nradulovic/hw_parvus/parvus_psu/spice_parvus_psu/ac-detect.asc

C1: cap; 4µ7
C2: cap; 4µ7
C3: cap; 10µ
C4: cap; 10µ
C5: cap; 10µ
C10: polcap; 10m; V=50 Irms=2.5 Rser=0.055 Lser=20n Rpar=40k Cpar=3p
C12: polcap; 10m; V=50 Irms=2.5 Rser=0.055 Lser=20n Rpar=40k Cpar=3p
C22: cap; 470n; Rser=700m Lser=7n Rpar=4.4meg Cpar=1p
C23: cap; 470n; Rser=700m Lser=7n Rpar=4.4meg Cpar=1p
D1: diode; 1N4148
D2: diode; 1N4148
D3: diode; 1N4148
D4: diode; 1N4148
D5: diode; 1N4148
D6: schottky; GBPC3502
D7: LED; QTLP690C
D9: schottky; GBPC3502
D10: schottky; GBPC3502
D11: schottky; GBPC3502
L4: ind; 4n; Rser=1m
L6: ind; 4n; Rser=1m
LGSPK2: ind2; {con1_len*17n}; Rser={con1_len*.5m}
LPWRGND: ind2; {con1_len*7n}; Rser={con1_len*.5m}
LVCC: ind2; {con1_len*7n}; Rser={con1_len*.5m}
LVEE: ind2; {con1_len*27n}; Rser={con1_len*.5m}
Q1: npn; BC546B
Q2: npn; BC546B
Q3: pnp; BC556B
Q4: pnp; BC556B
Q6: npn; BC546B
R1: res; 100k
R2: res; 10k
R3: res; 100k
R4: res; 100k
R5: res; 100
R6: res; {rser}
R7: res; {rser}
R8: res; {rser}
R9: res; {rser}
R10: res; 22k
R11: res; 22k
R12: res; 100k
R13: res; 22k
R14: res; 4k7
R15: res; 10k
R16: res; 2k
R17: res; 18k
R18: res; 25m
R26: res; 25m
R28: res; 15m
R38: res; 25m
R42: res; 10k
R45: res; .47
R46: res; 10k
R50: res; .47
S1: sw
S2: sw
V2: voltage; SINE(0 {supplyVLT*sqrt(2)} 50 1m 0 {phi}); Rser=0
V3: voltage; SINE(0 {supplyVLT*sqrt(2)} 50 1m 0 {phi}); Rser=0
V4: voltage; PULSE(0 20 200m 1n 1n 800m 1.2 2)
Named nets: vcc, vee, gspk, pwrgnd, 0, acs_p, acs_n, vsw, out, stby, mute
.op
.option plotwinsize=0
.option noopiter
Transient
.four {freq} 10 10 v(SPK+,SPK-)
.param prb=0
.param timestep={1/((65536/8)*freq)}
.param freq=50
.param stoptime {iterations/freq}
.ac oct 100 10 100meg
.step param prb list -1 1
AC analysis
.param iterations=80
.param Zimp=4
.param supplyPWR=40
.param supplyVLT=18
.param voutput={10*sqrt(2)}
.param supplyK 0.06
.param rser {(supplyVLT*supplyVLT*supplyK)/(2*supplyPWR)}
.tran 0 {stoptime} 100n {timestep}
.param phi=90
.param con1_len=5
.param con2_len 10
Konektor napajanja, star ground i napajanje
Ulazni parametri kola
.lib ../spice_root/lib/FCS_D.lib
.param BIAS=0.45
.param vinput voutput*(nfb1/nfb2)
.param nfb1=100
.param nfb2=1k5
.step temp 0 60 20
.model SW SW(Ron=1m Roff=1Meg Vt=18 Vh=1)
