nradulovic/hw_parvus/parvus_cmu/spice_parvus_cmu/dc_detect.asc

V1: voltage
V2: voltage
Named nets: 0, acp, acn
